flosean/JAFaR/jafar_sketch/rx5808.ino

/*
  This file is part of Fatshark© goggle rx module project (JAFaR).

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
    Copyright © 2016 Michele Martinelli
*/

//#include <Wire.h>
#include <EEPROM.h>
#include "rx5808.h"
#define RSSI_THRESH (scanVec[getMaxPos()]-5) //strong channels are near to the global max

RX5808::RX5808(uint8_t RSSIpin, uint8_t CSpin) {
  _rssiPin = RSSIpin;
  _csPin = CSpin;
  _stop_scan = 0;
}

uint16_t RX5808::getfrom_top8(uint8_t index) {
  return scanVecTop8[index];
}

void RX5808::compute_top8(void) {
  uint16_t scanVecTmp[CHANNEL_MAX];
  uint8_t _chan;

  memcpy(scanVecTmp, scanVec, sizeof(uint16_t)*CHANNEL_MAX);

  for (int8_t i = 7; i > 0; i--) {

    uint16_t maxVal = 0, maxPos = 0;
    for (_chan = CHANNEL_MIN; _chan < CHANNEL_MAX; _chan++) {
      if (maxVal < scanVecTmp[_chan]) { //new max
        maxPos = _chan;
        maxVal = scanVecTmp[_chan];
      }
    }

    //maxPos is the maximum
    scanVecTop8[i] = maxPos;
    scanVecTmp[maxPos] = 0;
  }
}

inline uint16_t RX5808::getRssiMin() {
  return rssi_min;
}

inline uint16_t RX5808::getRssiMax() {
  return rssi_max;
}

void RX5808::setRssiMax(uint16_t new_max) {
  rssi_max = new_max;
}

void RX5808::setRssiMin(uint16_t new_min) {
  rssi_min = new_min;
}

uint16_t RX5808::getRssi(uint16_t channel) {
  return scanVec[channel];
}

//stop scan
void RX5808::abortScan(void) {
  _stop_scan = 1;
}

//get the rssi value of a certain channel of a band and map it to 1...norm
uint16_t RX5808::getVal(uint16_t band, uint16_t channel, uint16_t norm) {
  uint16_t ret = constrain(scanVec[8 * band + channel], rssi_min, rssi_max);
  return map(ret, rssi_min, rssi_max, 0, norm);
}

//get the rssi value of a certain channel and map it to 1...norm
uint16_t RX5808::getVal(uint16_t pos, uint16_t norm) {
  uint16_t ret = constrain(scanVec[pos], rssi_min, rssi_max);
  return map(ret, rssi_min, rssi_max, 0, norm);
}

//get the maximum rssi value for a certain band and map it to 1...norm
uint16_t RX5808::getMaxValBand(uint8_t band, uint16_t norm) {
  uint16_t _chan;
  uint16_t maxVal = 0, maxPos = 8 * band;
  for (_chan = 8 * band; _chan < 8 * band + 8; _chan++) {
    if (maxVal < scanVec[_chan]) { //new max
      maxPos = _chan;
      maxVal = scanVec[_chan];
    }
  }

  maxVal = constrain(maxVal, rssi_min, rssi_max);
  return map(maxVal, rssi_min, rssi_max, 0, norm);
}

//get the channel with max rssi value for a certain band
uint16_t RX5808::getMaxPosBand(uint8_t band) {
  uint16_t _chan;
  uint16_t maxVal = 0, maxPos = 8 * band;
  for (_chan = 8 * band; _chan < 8 * band + 8; _chan++) {
    if (maxVal < scanVec[_chan]) { //new max
      maxPos = _chan;
      maxVal = scanVec[_chan];

    }
  }
  return maxPos;
}

//get the minimum rssi value for a certain band
uint16_t RX5808::getMinPosBand(uint8_t band) {
  uint16_t _chan;
  uint16_t minVal = 1000, minPos = 8 * band;
  for (_chan = 8 * band; _chan < 8 * band + 8; _chan++) {
    if (minVal > scanVec[_chan]) { //new max
      minPos = _chan;
      minVal = scanVec[_chan];

    }
  }
  return minPos;
}

//get global max
uint16_t RX5808::getMaxPos() {
  uint8_t _chan;
  uint16_t maxVal = 0, maxPos = 0;
  for (_chan = CHANNEL_MIN; _chan < CHANNEL_MAX; _chan++) {
    if (maxVal < scanVec[_chan]) { //new max
      maxPos = _chan;
      maxVal = scanVec[_chan];

    }
  }
  return maxPos;
}

//get global min
uint16_t RX5808::getMinPos() {
  uint8_t _chan;
  uint16_t minVal = 1000, minPos = 0;
  for (_chan = CHANNEL_MIN; _chan < CHANNEL_MAX; _chan++) {
    if (minVal > scanVec[_chan]) { //new max
      minPos = _chan;
      minVal = scanVec[_chan];

    }
  }
  return minPos;
}

uint16_t RX5808::getCurrentRSSI() {
  return _readRSSI();
}

void RX5808::init() {
  pinMode (_csPin, OUTPUT);
  pinMode (_rssiPin, INPUT);

  rssi_min = ((EEPROM.read(EEPROM_ADR_RSSI_MIN_H) << 8) | (EEPROM.read(EEPROM_ADR_RSSI_MIN_L)));
  rssi_max = ((EEPROM.read(EEPROM_ADR_RSSI_MAX_H) << 8) | (EEPROM.read(EEPROM_ADR_RSSI_MAX_L)));

  /*
    digitalWrite(_csPin, LOW);
    SPI.transfer(0x10);
    SPI.transfer(0x01);
    SPI.transfer(0x00);
    SPI.transfer(0x00);
    digitalWrite(_csPin, HIGH);
  */
  if (abs(rssi_max - rssi_min) > 300 || abs(rssi_max - rssi_min) < 50)
    calibration();

  scan();
}

//do a complete scan 
void RX5808::scan() {

  for (uint16_t _chan = CHANNEL_MIN; _chan < CHANNEL_MAX; _chan++) {
    if (_stop_scan) {
      _stop_scan = 0;
      return;
    }

    uint32_t freq = pgm_read_word_near(channelFreqTable + _chan);
    setFreq(freq);
    _wait_rssi();

    scanVec[_chan] = _readRSSI(); //raw value
  }
}

void RX5808::_wait_rssi() {
  // 30ms will to do a 32 channels scan in 1 second
#define MIN_TUNE_TIME 30
  delay(MIN_TUNE_TIME);
}

//simple avg of 4 value
uint16_t RX5808::_readRSSI() {
  volatile uint32_t sum = 0;
  delay(9);
  sum = analogRead(_rssiPin);
  sum += analogRead(_rssiPin);
  delay(1);
  sum += analogRead(_rssiPin);
  sum += analogRead(_rssiPin);
  return sum / 4.0;
}

//compute the min and max RSSI value and return them -> fast and inaccurate -> used for diversity module
void RX5808::setRSSIMinMax() {
  int i = 0;
  rssi_min = 1024;
  rssi_max = 0;

  scan(); //update rssi

  for (i = CHANNEL_MIN; i < CHANNEL_MAX; i++) {
    uint16_t rssi = scanVec[i];

    rssi_min = min(rssi_min, rssi);
    rssi_max = max(rssi_max, rssi);
  }

  return;
}

//compute the min and max RSSI value and store the values in EEPROM
void RX5808::calibration() {
  int i = 0, j = 0;
  uint16_t  rssi_setup_min = 1024, minValue = 1024;
  uint16_t  rssi_setup_max = 0, maxValue = 0;

  for (j = 0; j < 5; j++) {
    scan();

    for (i = CHANNEL_MIN; i < CHANNEL_MAX; i++) {
      uint16_t rssi = scanVec[i];

      minValue = min(minValue, rssi);
      maxValue = max(maxValue, rssi);
    }

    rssi_setup_min = min(rssi_setup_min, minValue); //?minValue:rssi_setup_min;
    rssi_setup_max = max(rssi_setup_max, maxValue); //?maxValue:rssi_setup_max;
  }

  // save 16 bit
  EEPROM.write(EEPROM_ADR_RSSI_MIN_L, (rssi_setup_min & 0xff));
  EEPROM.write(EEPROM_ADR_RSSI_MIN_H, (rssi_setup_min >> 8));
  // save 16 bit
  EEPROM.write(EEPROM_ADR_RSSI_MAX_L, (rssi_setup_max & 0xff));
  EEPROM.write(EEPROM_ADR_RSSI_MAX_H, (rssi_setup_max >> 8));

  rssi_min = ((EEPROM.read(EEPROM_ADR_RSSI_MIN_H) << 8) | (EEPROM.read(EEPROM_ADR_RSSI_MIN_L)));
  rssi_max = ((EEPROM.read(EEPROM_ADR_RSSI_MAX_H) << 8) | (EEPROM.read(EEPROM_ADR_RSSI_MAX_L)));


  // delay(1000);

  return;
}

void RX5808::setFreq(uint32_t freq) {
  uint8_t i;
  uint16_t channelData;

  uint32_t _if = (freq - 479);

  uint32_t N = floor(_if / 64);
  uint32_t A = floor((_if / 2) % 32);
  channelData = (N << 7) | (A & 0x7F);



  serialEnable(HIGH);
  delayMicroseconds(1);
  serialEnable(LOW);

  //REGISTER 1 - selection
  // bit bash out 25 bits of data
  // Order: A0-3, !R/W, D0-D19
  // A0=0, A1=0, A2=0, A3=1, RW=0, D0-19=0
  uint16_t reg1 = 0x10;
  for (i = 0; i < 25; i++)
    serialSendBit((reg1 >> i) & 1);

  // Clock the data in
  serialEnable(HIGH);
  delayMicroseconds(1);
  serialEnable(LOW);

  // Second is the channel data from the lookup table
  // 20 bytes of register data are sent, but the MSB 4 bits are zeros
  // register address = 0x1, write, data0-15=channelData data15-19=0x0
  serialEnable(HIGH);
  serialEnable(LOW);

  // Register 0x1
  serialSendBit(HIGH);
  serialSendBit(LOW);
  serialSendBit(LOW);
  serialSendBit(LOW);

  // Write to register
  serialSendBit(HIGH);

  // D0-D15
  //   note: loop runs backwards as more efficent on AVR
  for (i = 16; i > 0; i--) {
    serialSendBit(channelData & 0x1);
    // Shift bits along to check the next one
    channelData >>= 1;
  }

  // Remaining D16-D19
  for (i = 4; i > 0; i--)
    serialSendBit(LOW);

  // Finished clocking data in
  serialEnable(HIGH);
  delayMicroseconds(1);

  //  digitalWrite(_csPin, LOW);
  digitalWrite(spiClockPin, LOW);
  digitalWrite(spiDataPin, LOW);
}

void RX5808::serialSendBit(const uint8_t _b) {
  digitalWrite(spiClockPin, LOW);
  delayMicroseconds(1);

  digitalWrite(spiDataPin, _b);
  delayMicroseconds(1);
  digitalWrite(spiClockPin, HIGH);
  delayMicroseconds(1);

  digitalWrite(spiClockPin, LOW);
  delayMicroseconds(1);
}
void RX5808::serialEnable(const uint8_t _lev) {
  delayMicroseconds(1);
  digitalWrite(_csPin, _lev);
  delayMicroseconds(1);
}
